maxwolfs/rhizomatic-sublime/Presentation/Graphics/cloud.png

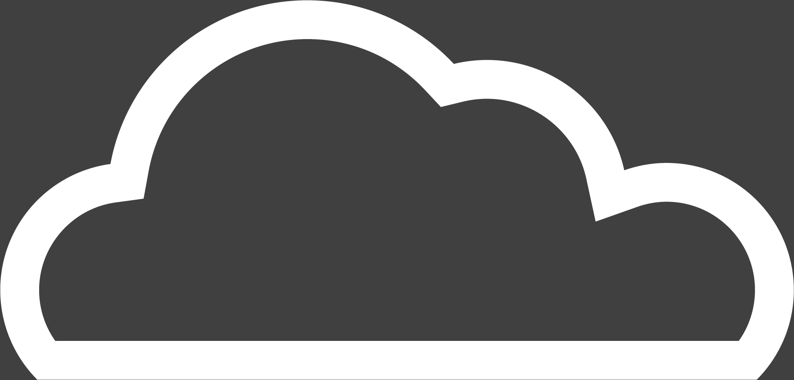
Presentation/Graphics/cloud.png
