maxwolfs/rhizomatic-sublime/Presentation/Graphics/kicad.PNG

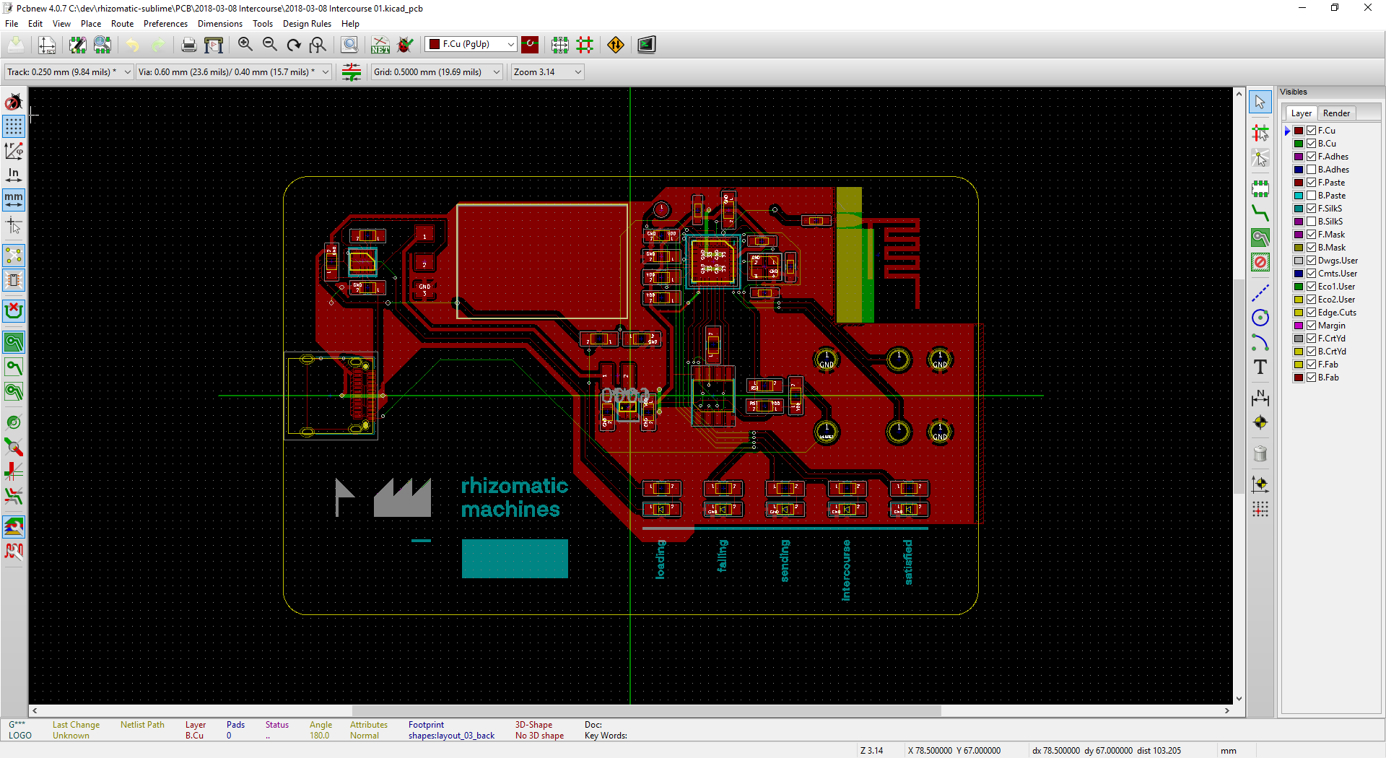
Presentation/Graphics/kicad.PNG
