maxwolfs/rhizomatic-sublime/PCB/2018-03-08 Intercourse/shapes/test-slk_02-01.png

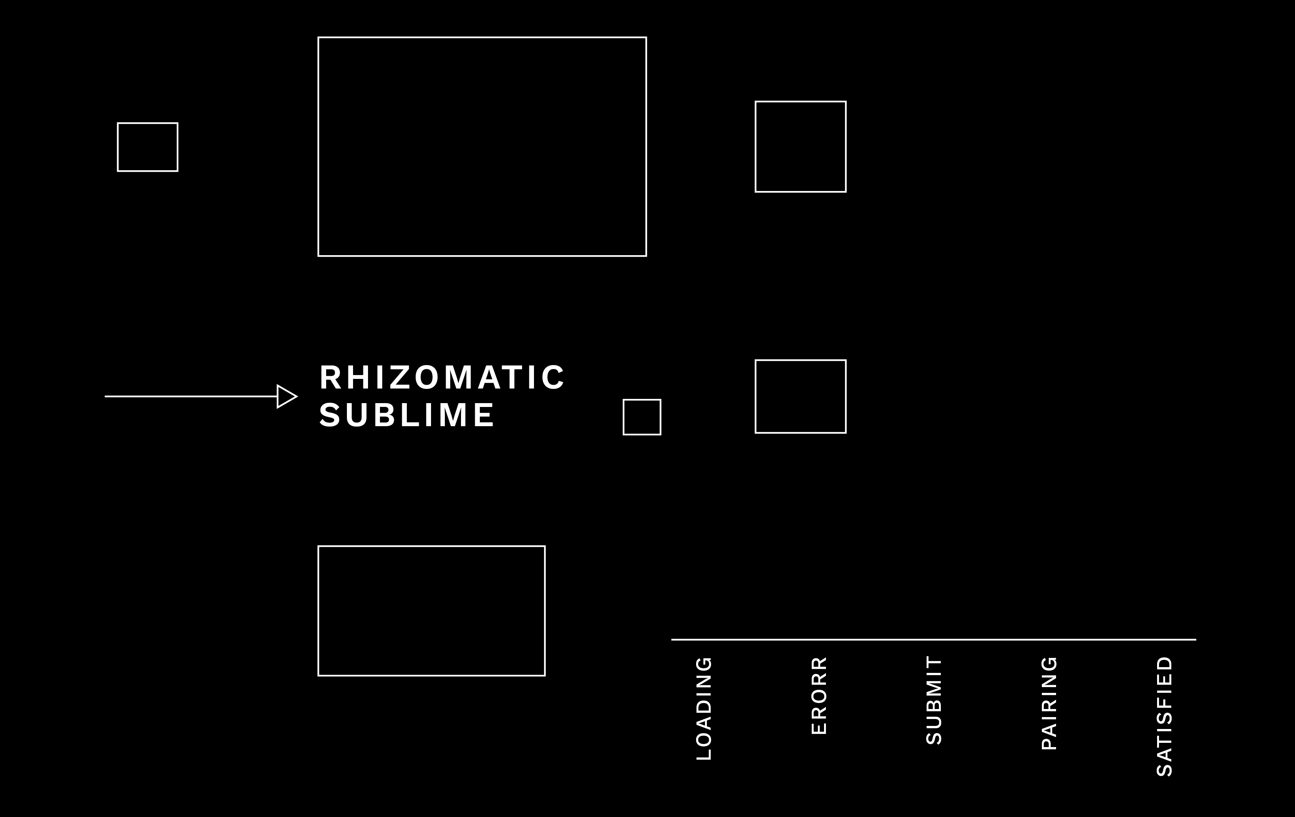
PCB/2018-03-08 Intercourse/shapes/test-slk_02-01.png
