maxwolfs/rhizomatic-sublime/PCB/2018-03-08 Intercourse/shapes/test-slk_02_back.png

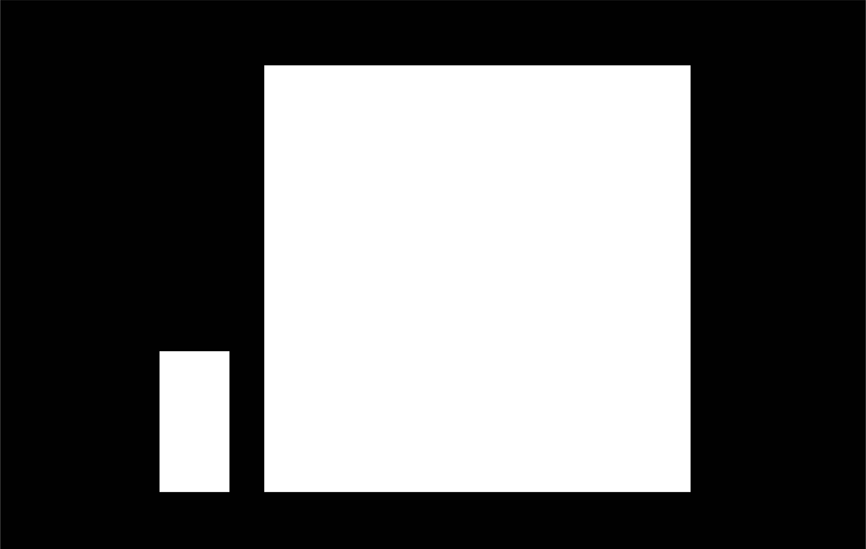
PCB/2018-03-08 Intercourse/shapes/test-slk_02_back.png
